vitormelon/esp32-pid-thermostat/src/timer_ctrl.h

#pragma once
#include <Arduino.h>

void timerInit();
void timerUpdate();
void timerStart();
void timerStop();
bool timerIsExpired();
void timerReset();
void timerResumeFromRecovery(unsigned long remainingMs);
